admmurph/savage_Klipper_Backup/printer_upgrades/kevinakasam_singleMotorBeltedZ/2_Bottom_F623_V3.7.stl

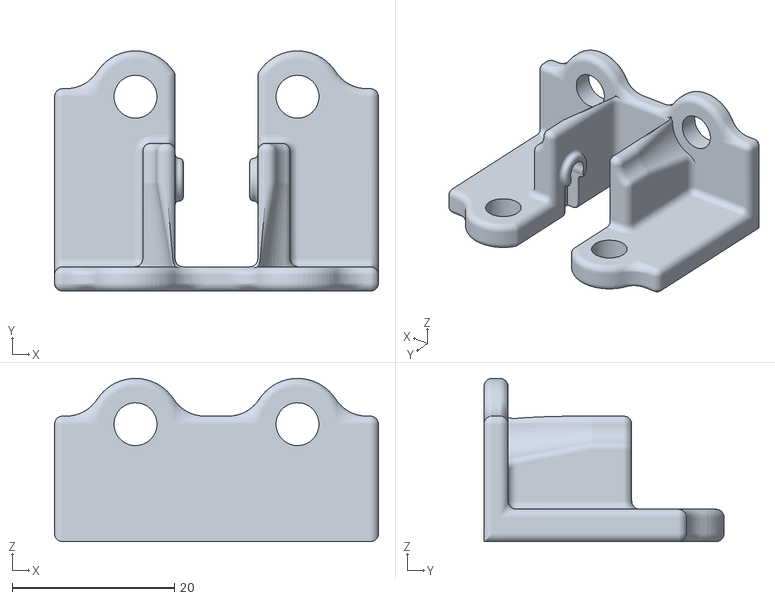
[picture p15: CAD file, 2025-01-03, last stored version]
printer_upgrades/kevinakasam_singleMotorBeltedZ/2_Bottom_F623_V3.7.stl
40.0 x 29.6 x 20.1
