admmurph/savage_Klipper_Backup/printer_upgrades/m5_webcam_arms/Ender_3_Webcam_Base_v2.stl

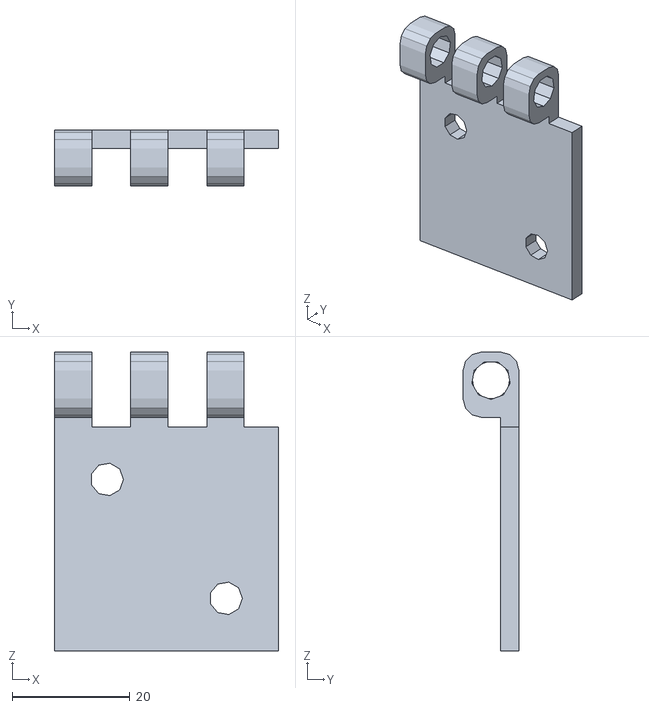
[picture p16: CAD file, 2025-01-03, last stored version]
printer_upgrades/m5_webcam_arms/Ender_3_Webcam_Base_v2.stl
38.1 x 9.52 x 50.8
