admmurph/savage_Klipper_Backup/printer_upgrades/qr_covers/Back_plate.stl

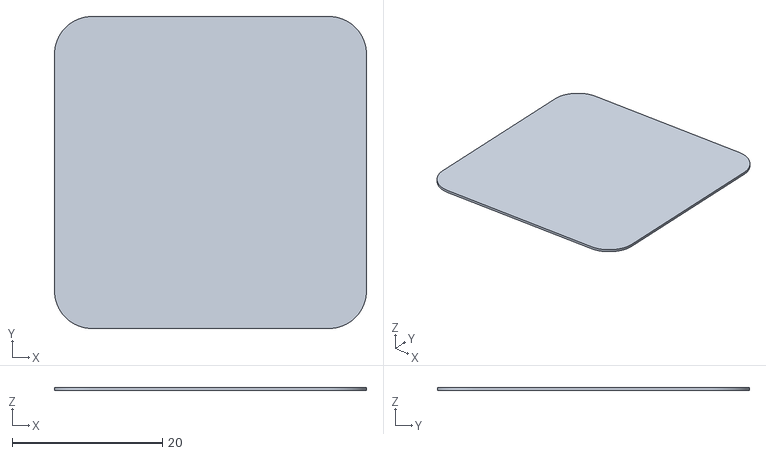
[picture p17: CAD file, 2025-01-03, last stored version]
printer_upgrades/qr_covers/Back_plate.stl
41.5 x 41.5 x 0.4
