admmurph/savage_Klipper_Backup/printer_upgrades/replacement_parts/Ender3_V2_belt_tensionerX.stl

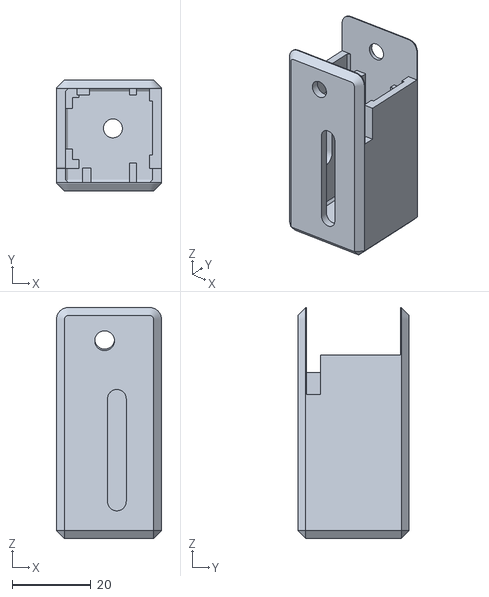
[picture p18: CAD file, 2025-01-03, last stored version]
printer_upgrades/replacement_parts/Ender3_V2_belt_tensionerX.stl
26.6 x 28.2 x 58.5
