admmurph/savage_Klipper_Backup/printer_upgrades/undercarriage/Mobo_Std_LM2596bucks+pi+80mm_fan.stl

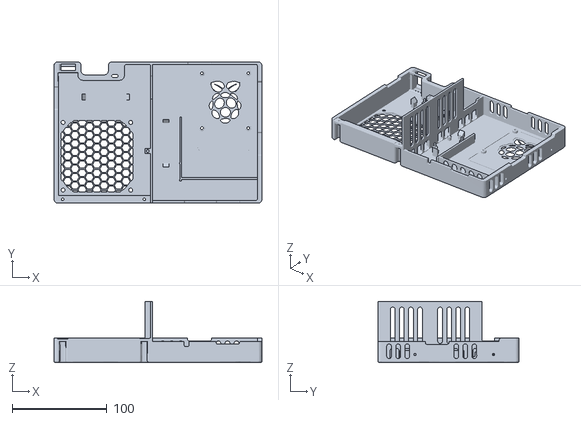
[picture p19: CAD file, 2025-01-03, last stored version]
printer_upgrades/undercarriage/Mobo_Std_LM2596bucks+pi+80mm_fan.stl
219.9 x 149.3 x 65.0
