admmurph/savage_Klipper_Backup/printer_upgrades/undercarriage/slim80mm psu/ContenVent2.stl

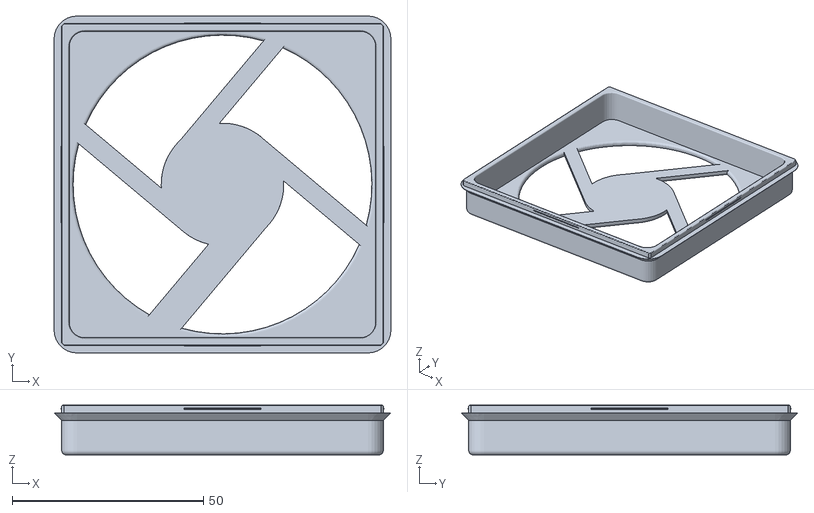
[picture p20: CAD file, 2025-01-03, last stored version]
printer_upgrades/undercarriage/slim80mm psu/ContenVent2.stl
88.0 x 88.0 x 13.0
