admmurph/savage_Klipper_Backup/printer_upgrades/ducts/apollo/bowden adapter - orbiter 2 rear motor backplate.stl

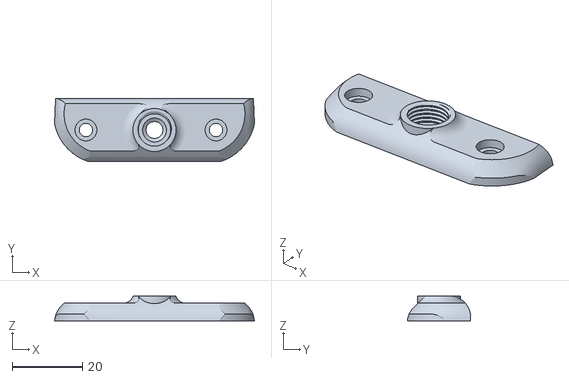
[picture p21: CAD file, 2025-01-03, last stored version]
printer_upgrades/ducts/apollo/bowden adapter - orbiter 2 rear motor backplate.stl
56.9 x 18.0 x 7.00
