admmurph/savage_Klipper_Backup/printer_upgrades/extras/Ender 3 bed leveling wheel clips v2 thicker armsflipped.stl

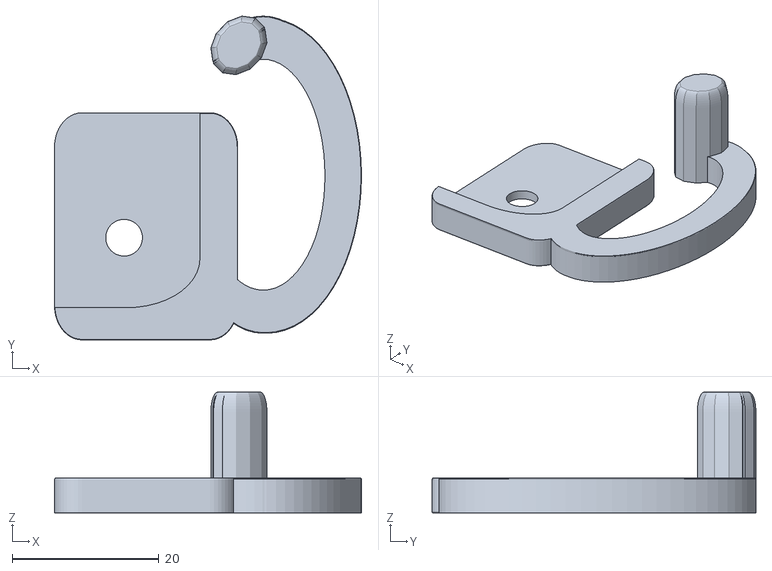
[picture p22: CAD file, 2025-01-03, last stored version]
printer_upgrades/extras/Ender 3 bed leveling wheel clips v2 thicker armsflipped.stl
41.9 x 44.2 x 16.5
