admmurph/savage_Klipper_Backup/printer_upgrades/filament_holders/Roller/Shaft_80mm.stl

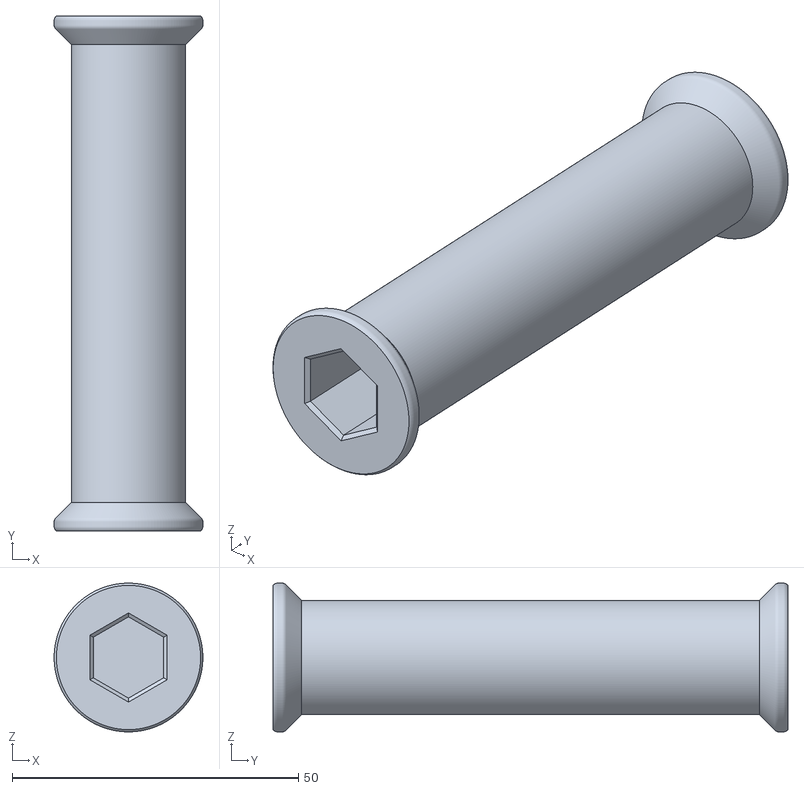
[picture p23: CAD file, 2025-01-03, last stored version]
printer_upgrades/filament_holders/Roller/Shaft_80mm.stl
26.0 x 90.0 x 26.0
