admmurph/savage_Klipper_Backup/printer_upgrades/kevinakasam_singleMotorBeltedZ/1_RightV3.7.stl

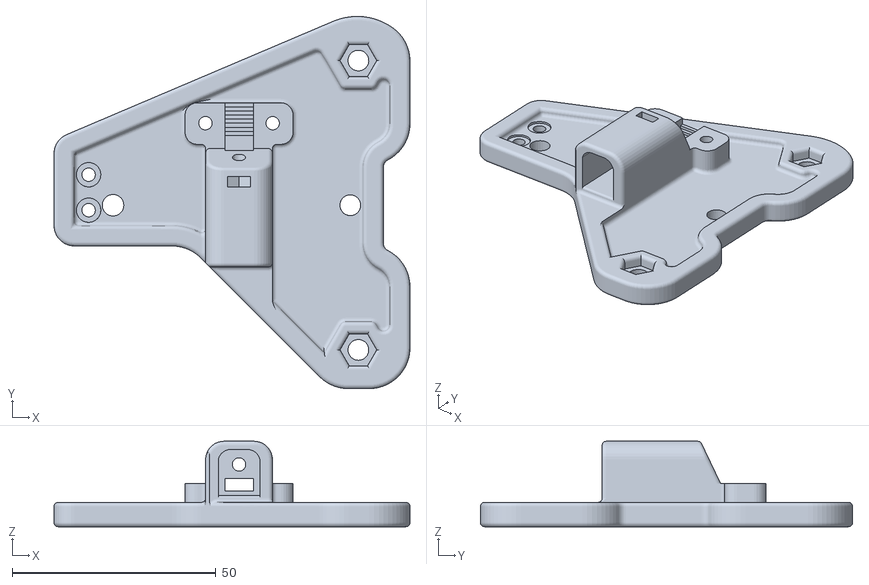
[picture p24: CAD file, 2025-01-03, last stored version]
printer_upgrades/kevinakasam_singleMotorBeltedZ/1_RightV3.7.stl
87.4 x 91.3 x 21.0
