admmurph/savage_Klipper_Backup/printer_upgrades/ducts/apollo/CRtouch - baseline.stl

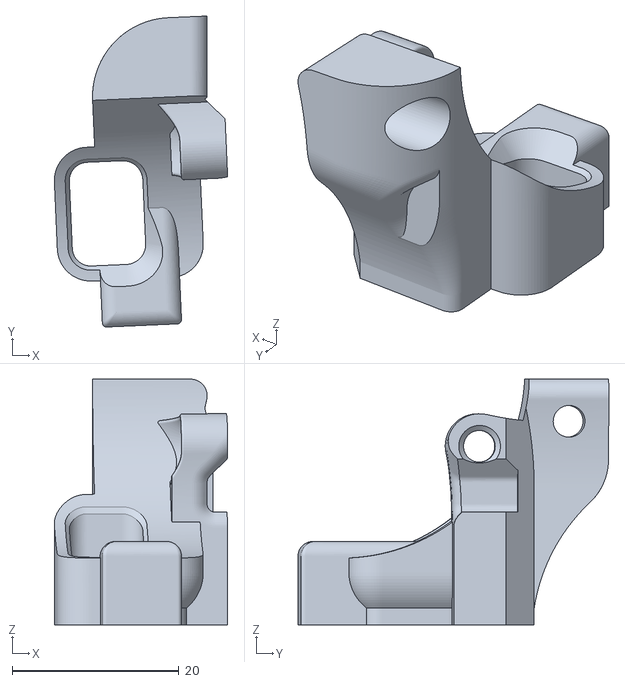
[picture p25: CAD file, 2025-01-03, last stored version]
printer_upgrades/ducts/apollo/CRtouch - baseline.stl
20.8 x 37.3 x 29.4
