admmurph/savage_Klipper_Backup/printer_upgrades/filament_holders/Roller/Threaded_Clip45deg.stl

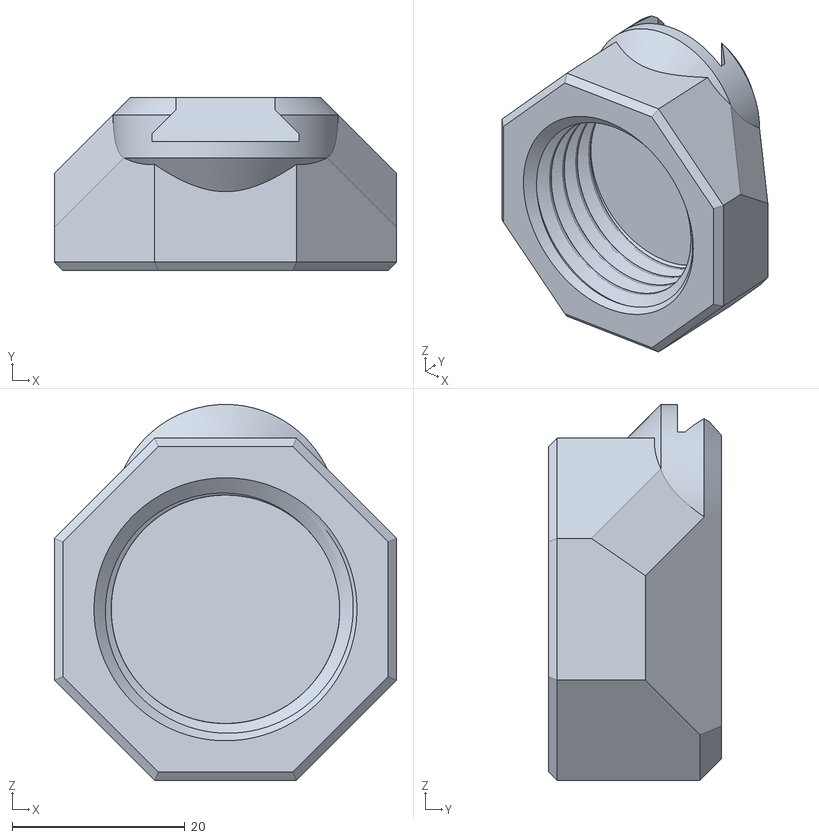
[picture p26: CAD file, 2025-01-03, last stored version]
printer_upgrades/filament_holders/Roller/Threaded_Clip45deg.stl
39.6 x 20.0 x 43.5
