admmurph/savage_Klipper_Backup/printer_upgrades/ducts/apollo/left duct - baseline.stl

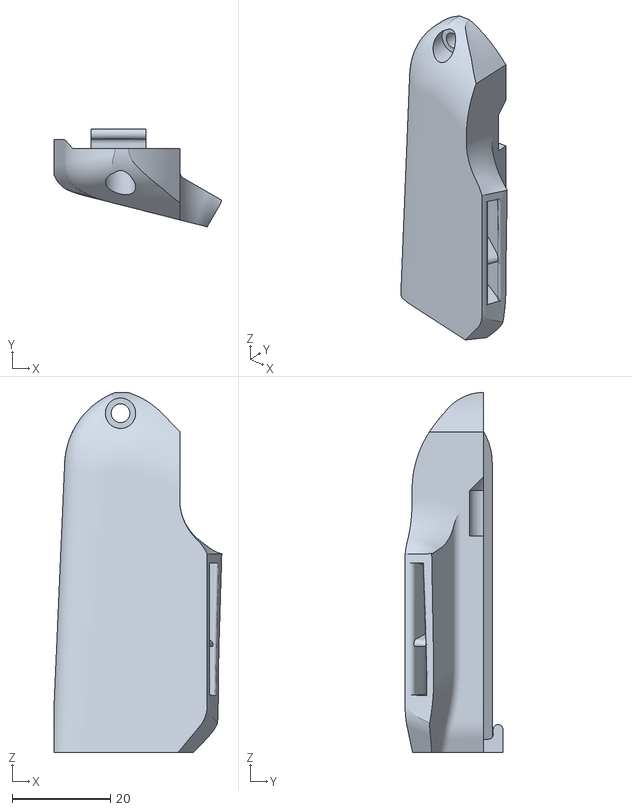
[picture p28: CAD file, 2025-01-03, last stored version]
printer_upgrades/ducts/apollo/left duct - baseline.stl
34.2 x 19.9 x 73.4
