admmurph/savage_Klipper_Backup/printer_upgrades/extras/MinimalBedHandle.stl

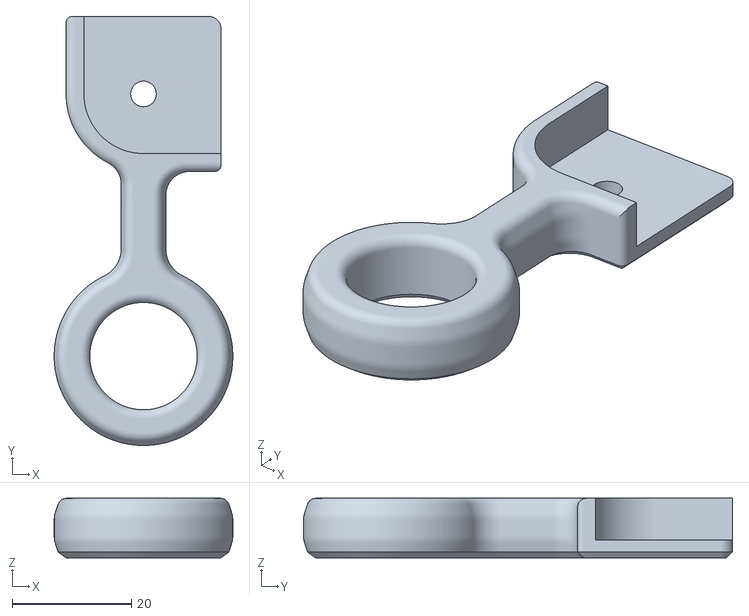
[picture p29: CAD file, 2025-01-03, last stored version]
printer_upgrades/extras/MinimalBedHandle.stl
30.0 x 72.0 x 10.0
