admmurph/savage_Klipper_Backup/printer_upgrades/filament_holders/Roller/Shaft_75mm.stl

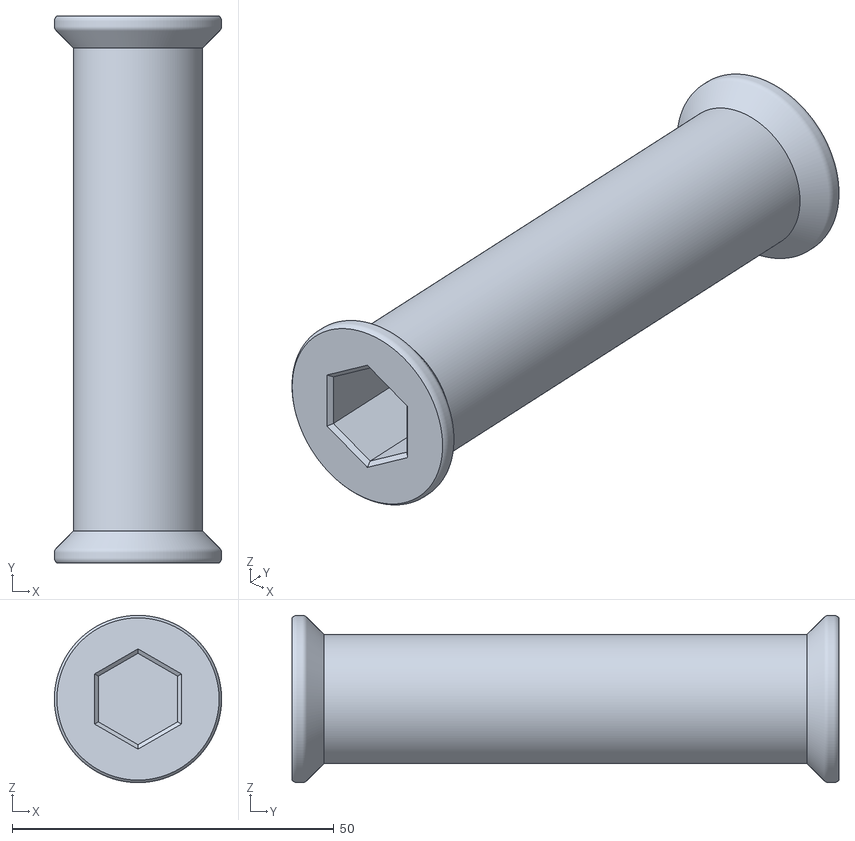
[picture p30: CAD file, 2025-01-03, last stored version]
printer_upgrades/filament_holders/Roller/Shaft_75mm.stl
26.0 x 85.0 x 26.0
