admmurph/savage_Klipper_Backup/printer_upgrades/kevinakasam_singleMotorBeltedZ/3_Spacer2.stl

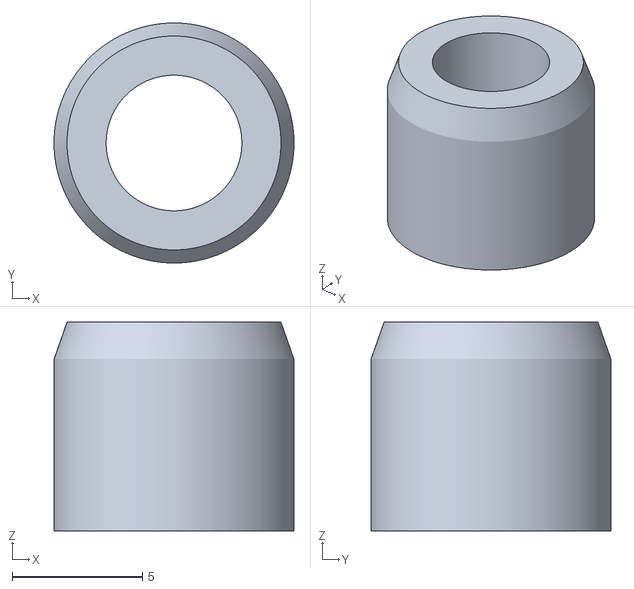
[picture p31: CAD file, 2025-01-03, last stored version]
printer_upgrades/kevinakasam_singleMotorBeltedZ/3_Spacer2.stl
9.20 x 9.20 x 8.00
