admmurph/savage_Klipper_Backup/printer_upgrades/extras/chungy_knob.stl

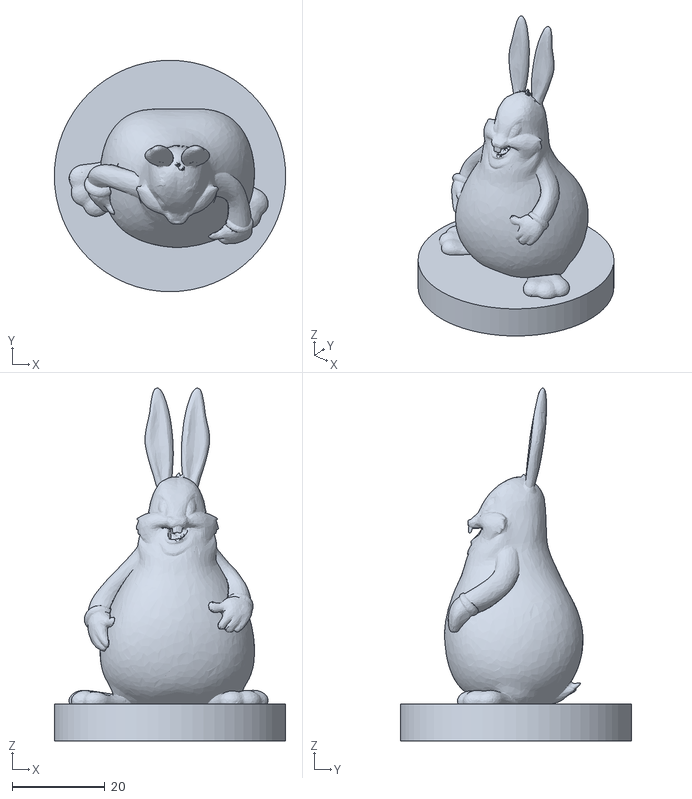
[picture p33: CAD file, 2025-01-03, last stored version]
printer_upgrades/extras/chungy_knob.stl
50.0 x 50.0 x 76.3
