admmurph/savage_Klipper_Backup/printer_upgrades/filament_holders/Roller/Shaft_90mm.stl

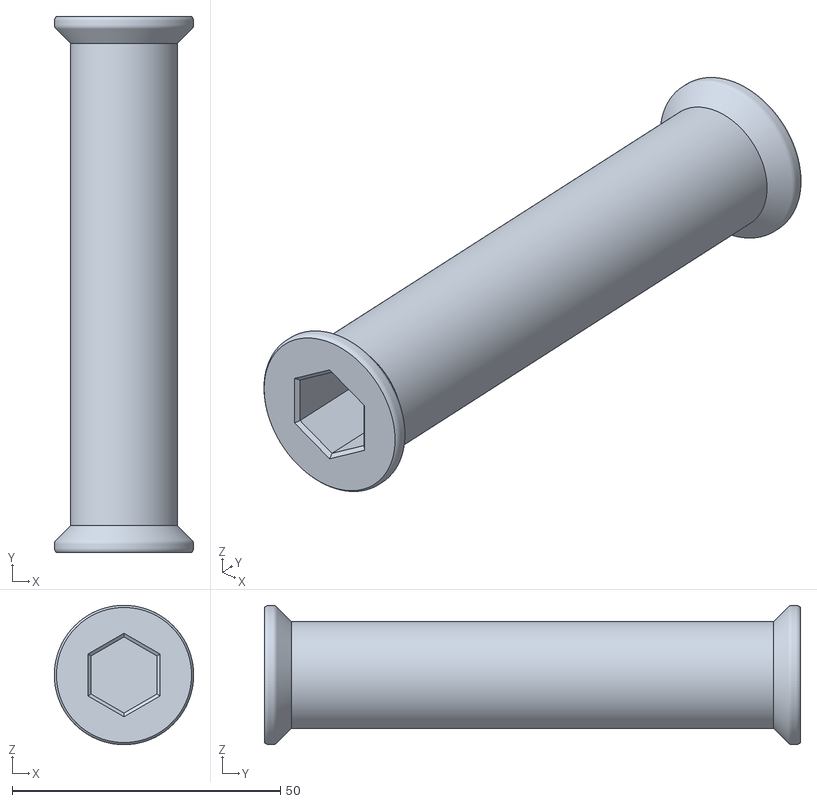
[picture p34: CAD file, 2025-01-03, last stored version]
printer_upgrades/filament_holders/Roller/Shaft_90mm.stl
26.0 x 100.0 x 26.0
