admmurph/savage_Klipper_Backup/printer_upgrades/kevinakasam_singleMotorBeltedZ/1_Power_Supply_Holder.stl

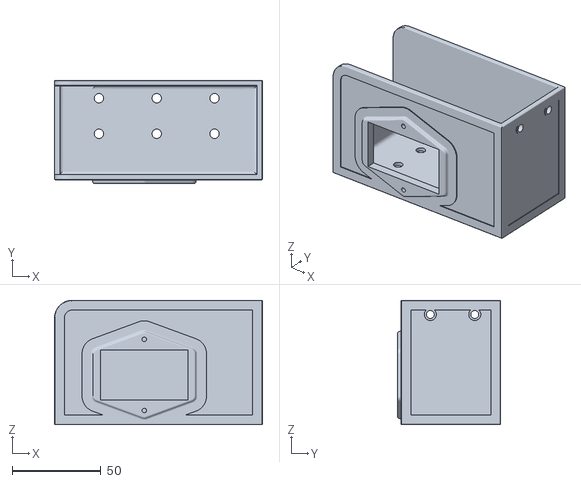
[picture p35: CAD file, 2025-01-03, last stored version]
printer_upgrades/kevinakasam_singleMotorBeltedZ/1_Power_Supply_Holder.stl
117.0 x 58.0 x 70.0
