admmurph/savage_Klipper_Backup/printer_upgrades/ducts/apollo/Orbiter 1.5 - Creality - stock MK8.stl

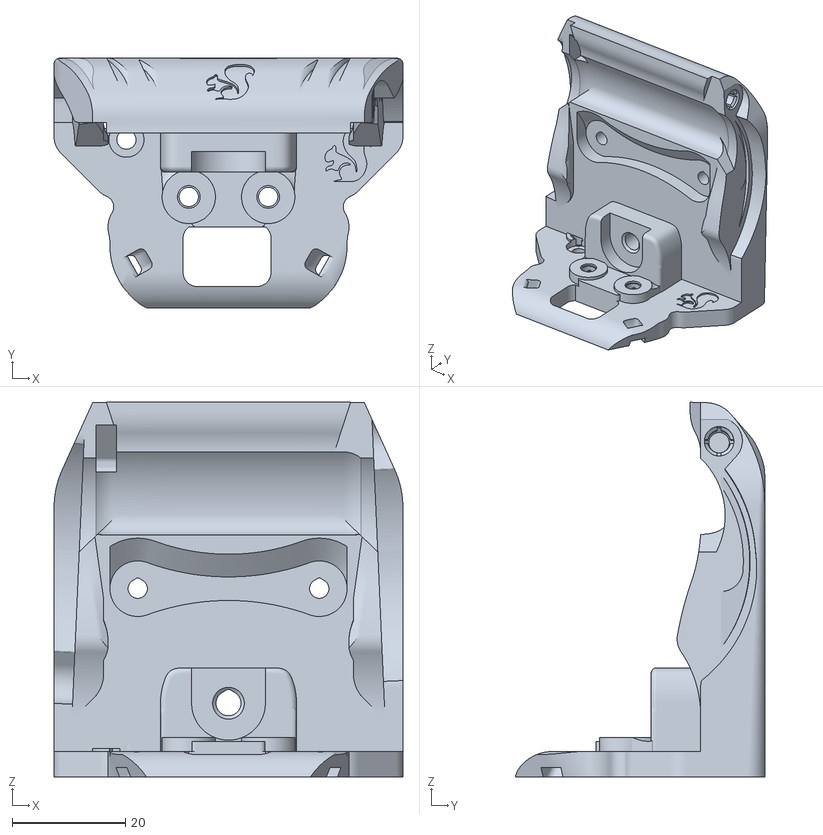
[picture p36: CAD file, 2025-01-03, last stored version]
printer_upgrades/ducts/apollo/Orbiter 1.5 - Creality - stock MK8.stl
61.5 x 44.0 x 66.1
