admmurph/savage_Klipper_Backup/printer_upgrades/filament_holders/Roller/Shaft_100mm.stl

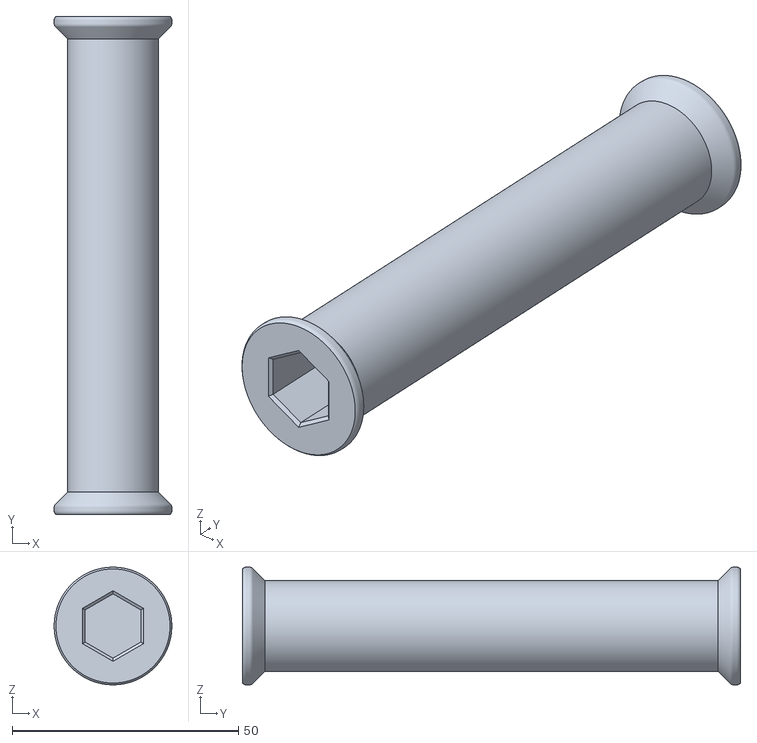
[picture p37: CAD file, 2025-01-03, last stored version]
printer_upgrades/filament_holders/Roller/Shaft_100mm.stl
26.0 x 110.0 x 26.0
