admmurph/savage_Klipper_Backup/printer_upgrades/kevinakasam_singleMotorBeltedZ/1_RightTop_UL_V3.6.stl

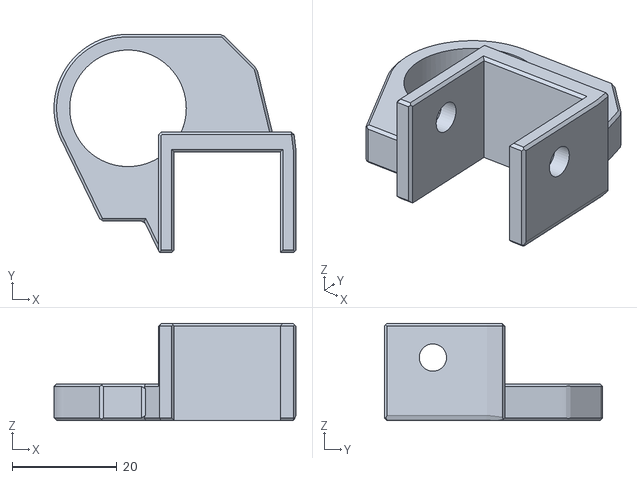
[picture p38: CAD file, 2025-01-03, last stored version]
printer_upgrades/kevinakasam_singleMotorBeltedZ/1_RightTop_UL_V3.6.stl
46.1 x 41.6 x 18.5
