admmurph/savage_Klipper_Backup/printer_upgrades/filament_holders/Roller/Body_75mm.stl

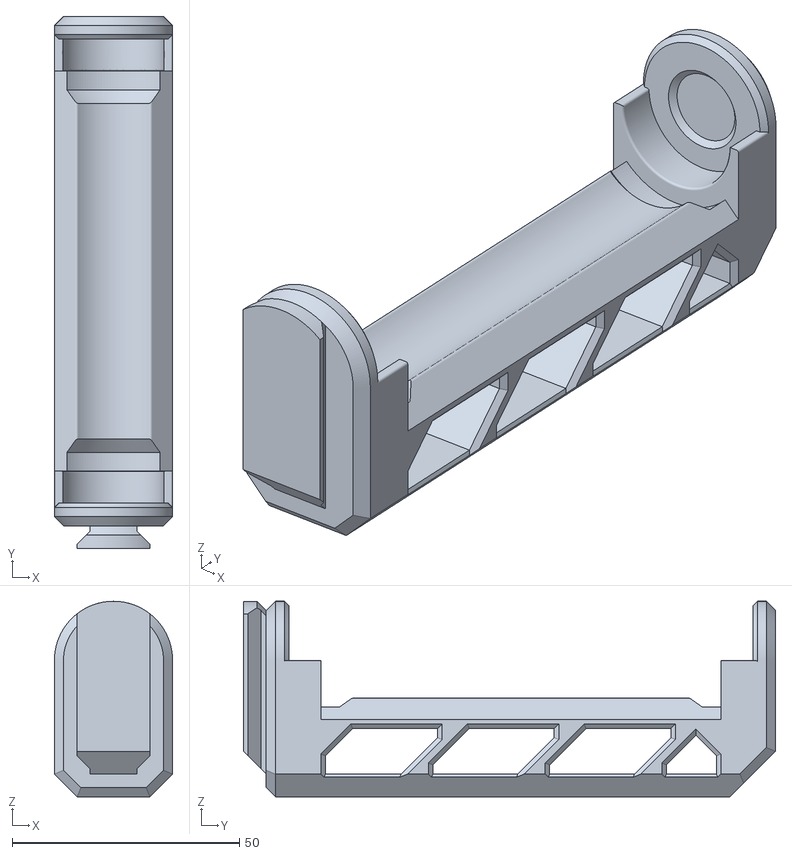
[picture p39: CAD file, 2025-01-03, last stored version]
printer_upgrades/filament_holders/Roller/Body_75mm.stl
26.0 x 117.0 x 43.0
