admmurph/savage_Klipper_Backup/printer_upgrades/filament_holders/Roller/Body_90mm.stl

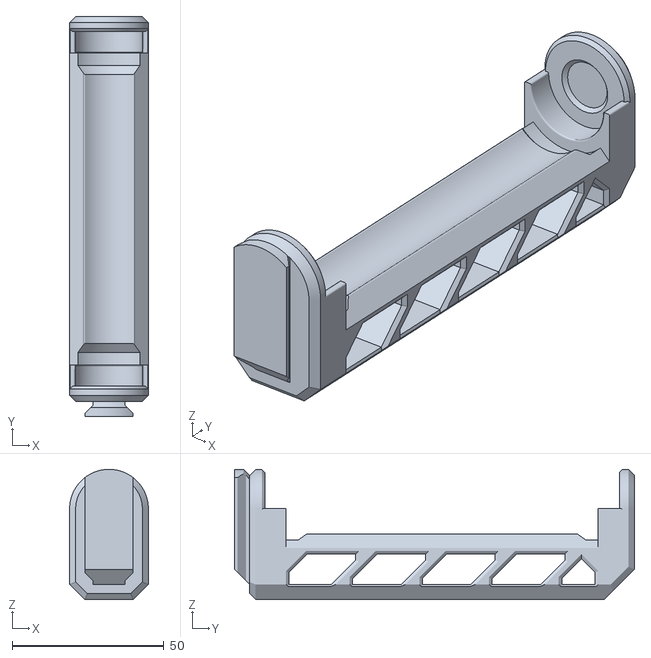
[picture p41: CAD file, 2025-01-03, last stored version]
printer_upgrades/filament_holders/Roller/Body_90mm.stl
26.0 x 132.0 x 43.0
