admmurph/savage_Klipper_Backup/printer_upgrades/kevinakasam_singleMotorBeltedZ/2_TensionerClampV3.stl

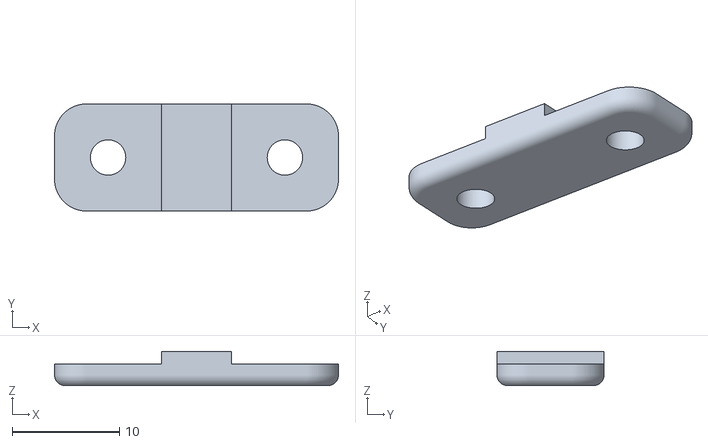
[picture p42: CAD file, 2025-01-03, last stored version]
printer_upgrades/kevinakasam_singleMotorBeltedZ/2_TensionerClampV3.stl
26.5 x 10.0 x 3.20
