admmurph/savage_Klipper_Backup/printer_upgrades/filament_holders/Roller/Mounting_Clip.stl

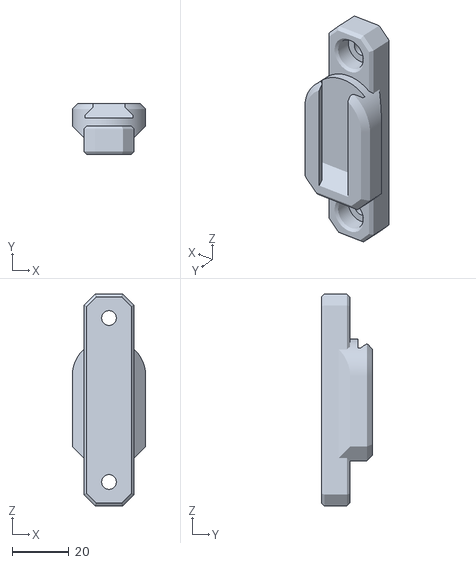
[picture p43: CAD file, 2025-01-03, last stored version]
printer_upgrades/filament_holders/Roller/Mounting_Clip.stl
26.0 x 18.0 x 75.0
