admmurph/savage_Klipper_Backup/printer_upgrades/kevinakasam_singleMotorBeltedZ/1_Transmission_UL_V3.7.stl

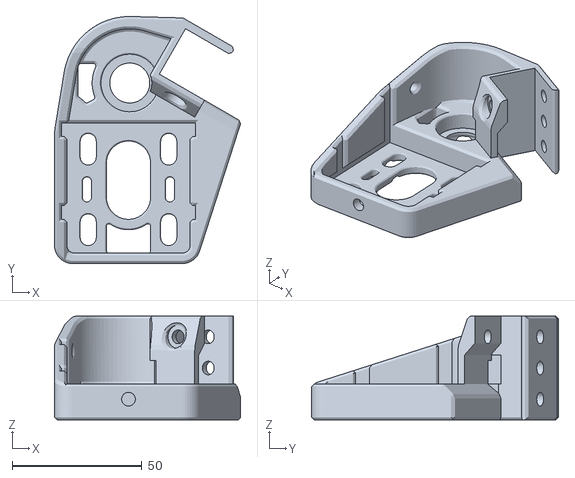
[picture p44: CAD file, 2025-01-03, last stored version]
printer_upgrades/kevinakasam_singleMotorBeltedZ/1_Transmission_UL_V3.7.stl
71.7 x 95.1 x 40.0
