admmurph/savage_Klipper_Backup/printer_upgrades/filament_holders/Roller/ThreadedClip22.5deg.STL

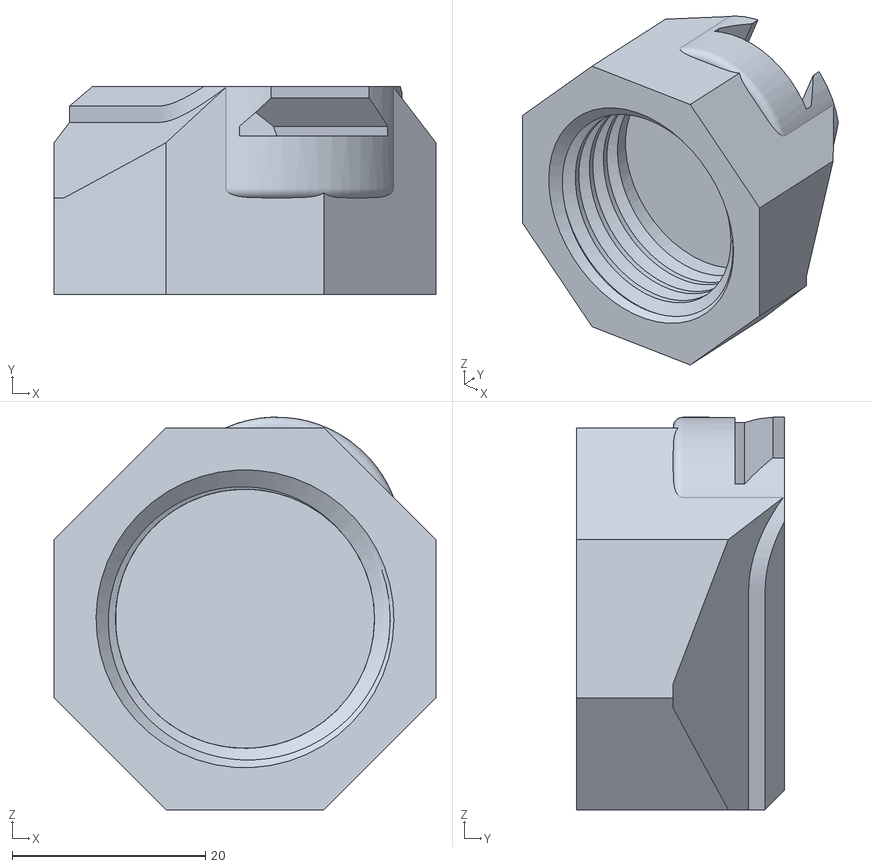
[picture p45: CAD file, 2025-01-03, last stored version]
printer_upgrades/filament_holders/Roller/ThreadedClip22.5deg.STL
39.5 x 21.5 x 40.6
