admmurph/savage_Klipper_Backup/printer_upgrades/kevinakasam_singleMotorBeltedZ/1_MotorMountTensionerArm_V3.6.stl

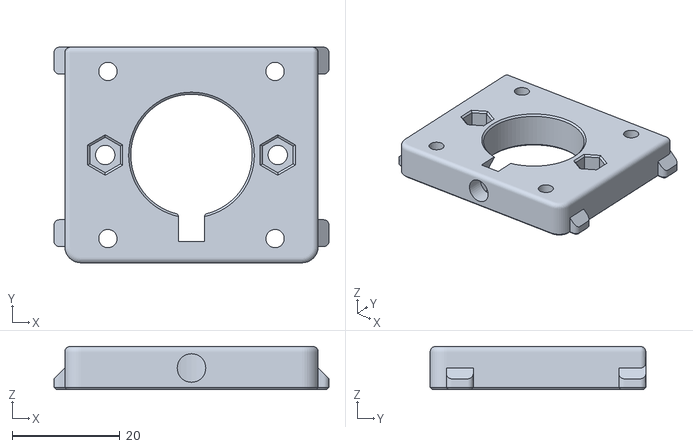
[picture p46: CAD file, 2025-01-03, last stored version]
printer_upgrades/kevinakasam_singleMotorBeltedZ/1_MotorMountTensionerArm_V3.6.stl
51.0 x 40.0 x 8.00
