admmurph/savage_Klipper_Backup/printer_upgrades/filament_holders/Roller/Body_100mm.stl

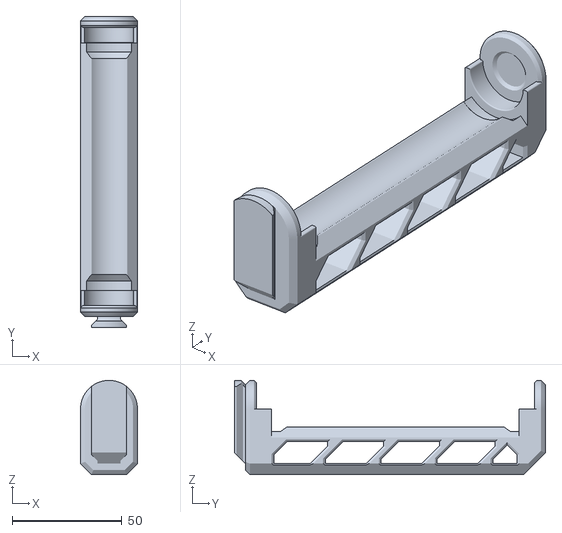
[picture p47: CAD file, 2025-01-03, last stored version]
printer_upgrades/filament_holders/Roller/Body_100mm.stl
26.0 x 142.0 x 43.0
