admmurph/savage_Klipper_Backup/printer_upgrades/kevinakasam_singleMotorBeltedZ/2_TensionerBlockV3.stl

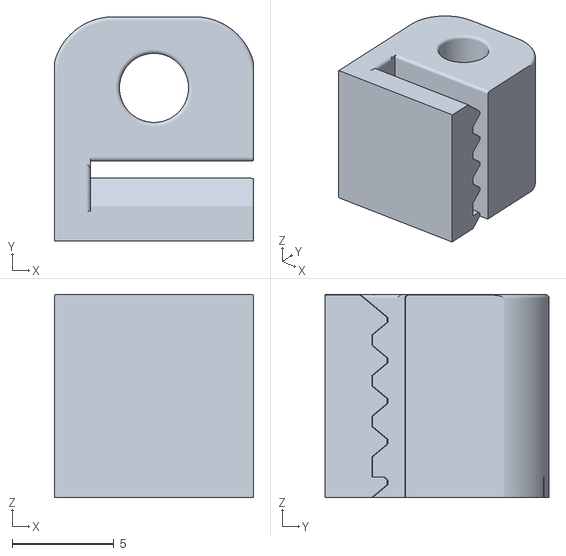
[picture p48: CAD file, 2025-01-03, last stored version]
printer_upgrades/kevinakasam_singleMotorBeltedZ/2_TensionerBlockV3.stl
9.80 x 11.0 x 10.00
